rodan/eecu-sat/ltspice/buffy_test.asc

D1: zener
D2: schottky
R1: res; 10k
R2: res; 10K
R3: res; 10k
R4: res; 5K
U1: OP27
V1: voltage; 15
V2: voltage; 5
V3: voltage; SINE(5 5 100000)
Named nets: 0, v+, v-, in, out
.lib tl72.lib
.tran 0.0001s
stage 1
gain: 10.170
freq: 663.146
Q: 0.500
GBW reqd: 331.75
topology: single pole
