rodan/eecu-sat/ltspice/buffy.asc

D1: zener
D2: schottky
R1: res; 10k
R2: res; 10K
R3: res; 10k
R4: res; 5K
U1: OP27
V1: voltage; 15
V2: voltage; 15
V3: voltage; ""; AC 10
Named nets: 0, v+, v-, in, out
.lib tl72.lib
.ac lin 1000 100 10000000
stage 1
gain: 10.170
freq: 663.146
Q: 0.500
GBW reqd: 331.75
topology: single pole
