rodan/eecu-sat/software/eecu-sat/output_srzip.c

/*
 * This file is part of the eecu-sat project.
 *
 * Copyright (C) 2024 Petre Rodan <2b4eda@subdimension.ro>
 *
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
 * You should have received a copy of the GNU General Public License
 * along with this program.  If not, see <http://www.gnu.org/licenses/>.
 */

#include <stdlib.h>
#include <stdint.h>
#include <unistd.h>
#include <stdbool.h>
#include <zip.h>
#include "proj.h"
#include "error.h"
#include "output.h"

struct out_context {
    char *target_filename;      // filename within the archive
    char *metadata_file;
};

static int init(struct sr_output *o, GHashTable *options)
{
    struct zip_source *src;
    struct zip_source *metadata = NULL;
    struct zip *archive;
    struct out_context *outc;
    GSList *l;
    char *buff = NULL;
    char buffl[LINE_MAX_SZ];
    ssize_t i;
    ch_data_t *ch_data_ptr;

    unlink(o->filename);

    outc = (struct out_context *)g_malloc0(sizeof(struct out_context));
    o->priv = outc;

    /* Options */
    outc->metadata_file = g_strdup(g_variant_get_string(g_hash_table_lookup(options, "metadata_file"), NULL));

    outc->target_filename = (char *)g_malloc0(PATH_MAX);

    archive = zip_open(o->filename, ZIP_CREATE, NULL);
    if (!archive) {
        err_msg("%s:%d error: zip_open() has failed", __FILE__, __LINE__);
        return SR_ERR_IO;
    }

    src = zip_source_buffer(archive, "2", 1, 0);
    if (zip_file_add(archive, "version", src, ZIP_FL_ENC_UTF_8) < 0) {
        err_msg("%s:%d Error adding file into archive: %s", __FILE__, __LINE__, zip_strerror(archive));
        zip_source_free(src);
        zip_discard(archive);
        return SR_ERR_IO;
    }

    if (outc->metadata_file && (outc->metadata_file[0] != 0)) {
        metadata = zip_source_file(archive, outc->metadata_file, 0, -1);
        if (!metadata) {
            err_msg("%s:%d Error adding file into archive: %s", __FILE__, __LINE__, zip_strerror(archive));
            return SR_ERR_IO;
        }
        if (zip_file_add(archive, "metadata", metadata, ZIP_FL_ENC_UTF_8) < 0) {
            err_msg("%s:%d Error adding file into archive: %s", __FILE__, __LINE__, zip_strerror(archive));
            zip_source_free(metadata);
            zip_discard(archive);
            return SR_ERR_IO;
        }
    } else {
        buff = g_malloc0(4096);
        strcat(buff, "[global]\nsigrok version=0.5.2\n\n[device 1]\n");
        l = o->sdi->channels;
        ch_data_ptr = l->data;
        snprintf(buffl, LINE_MAX_SZ, "samplerate=%ld Hz\n", ch_data_ptr->header.sample_rate / ch_data_ptr->header.downsample);
        strcat(buff, buffl);
        snprintf(buffl, LINE_MAX_SZ, "total analog=%d\n", g_slist_length(o->sdi->channels));
        strcat(buff, buffl);
        i=0;
        for (l = o->sdi->channels; l; l = l->next) {
            i++;
            snprintf(buffl, LINE_MAX_SZ, "analog%ld=CH%ld\n", i, i);
            strcat(buff, buffl);
        }
        metadata = zip_source_buffer(archive, buff, strlen(buff), 0);
        if (zip_file_add(archive, "metadata", metadata, ZIP_FL_ENC_UTF_8) < 0) {
            err_msg("%s:%d Error adding file into archive: %s", __FILE__, __LINE__, zip_strerror(archive));
            zip_source_free(metadata);
            zip_discard(archive);
            g_free(buff);
            return SR_ERR_IO;
        }
    }

    if (zip_close(archive) < 0) {
        err_msg("%s:%d Error saving zipfile: %s", __FILE__, __LINE__, zip_strerror(archive));
        zip_discard(archive);
        return SR_ERR_IO;
    }

    if (buff)
        g_free(buff);

    return SR_OK;
}

static int receive(const struct sr_output *o, const struct sr_datafeed_packet *pkt, GString **out)
{
    struct zip *archive;
    struct zip_source *src;
    struct out_context *outc = o->priv;
    const struct sr_datafeed_analog *analog;
    const struct sat_generic_pkt *gpkt;
    const struct dev_frame *frame = o->sdi->priv;

    UNUSED(out);

    if (!(archive = zip_open(o->filename, 0, NULL)))
        return SR_ERR_IO;

    switch (pkt->type) {
    case SR_DF_META:
        gpkt = pkt->payload;
        src = zip_source_buffer(archive, gpkt->payload, gpkt->payload_sz, 0);
        snprintf(outc->target_filename, PATH_MAX - 1, "metadata");
        break;
    case SR_DF_ANALOG:
        analog = pkt->payload;
        src = zip_source_buffer(archive, analog->data, analog->num_samples * sizeof(float), 0);
        snprintf(outc->target_filename, PATH_MAX - 1, "analog-1-%d-%d", frame->ch, frame->chunk);
        break;
    default:
        goto cleanup;
    }

    if (zip_file_add(archive, outc->target_filename, src, ZIP_FL_ENC_UTF_8) < 0) {
        err_msg("%s:%d Failed to add chunk: %s", __FILE__, __LINE__, zip_strerror(archive));
        zip_source_free(src);
        zip_discard(archive);
        return SR_ERR_IO;
    }

 cleanup:
    if (zip_close(archive) < 0) {
        err_msg("%s:%d Error saving session file: %s", __FILE__, __LINE__, zip_strerror(archive));
        zip_discard(archive);
        return SR_ERR_IO;
    }

    return SR_OK;
}

static struct sr_option options[] = {
    {"metadata_file", "metadata file", "custom metadata file to include in the output srzip archive", NULL, NULL},
	ALL_ZERO
};

static const struct sr_option *get_options(void)
{
    if (!options[0].def) {
        options[0].def = g_variant_ref_sink(g_variant_new_string(""));
    }

	return options;
}

static int cleanup(struct sr_output *o)
{
    struct out_context *outc;

    if (o == NULL)
        return SR_ERR_BUG;

    if (o->priv) {
        outc = o->priv;
        if (outc->target_filename)
            g_free(outc->target_filename);
        if (outc->metadata_file)
            g_free(outc->metadata_file);

        g_free(o->priv);
    }

    return SR_OK;
}

struct sr_output_module output_srzip = {
    .id = "srzip",
    .name = "srzip",
    .desc = "sigrok session file format data",
    .exts = (const char *[]) {"sr", NULL},
    .flags = SR_OUTPUT_INTERNAL_IO_HANDLING,
    .options = get_options,
    .init = init,
    .receive = receive,
    .cleanup = cleanup,
};
